bechhansen/wattzig/Software/main/kamstrup_test_data.h

#ifndef KAMSTRUP_TEST_DATA_H
#define KAMSTRUP_TEST_DATA_H

#include <stdint.h>
#include <stddef.h>

/**
 * @file kamstrup_test_data.h
 * @brief Test data for Kamstrup power meter simulation
 * 
 * This file contains example DLMS/COSEM data from a Kamstrup power meter
 * for testing and development purposes.
 */

// Test data - Kamstrup DLMS message example
static const uint8_t kamstrup_test_data[] = {
    0x7E, 0xA1, 0x2C, 0x2B, 0x21, 0x13, 0xFC, 0x04, 0xE6, 0xE7, 0x00,
    0x0F, 0x00, 0x00, 0x00, 0x00, 0x0C, 0x07, 0xE1, 0x08, 0x10, 0x03, 0x10, 0x00, 0x05, 0xFF, 0x80, 0x00, 0x00,
    0x02, 0x23,
    0x0A, 0x0E, 0x4B, 0x61, 0x6D, 0x73, 0x74, 0x72, 0x75, 0x70, 0x5F, 0x56, 0x30, 0x30, 0x30, 0x31,
    0x09, 0x06, 0x01, 0x01, 0x00, 0x00, 0x05, 0xFF, 0x0A, 0x10, 0x35, 0x37, 0x30, 0x36, 0x35, 0x36, 0x37, 0x30, 0x30, 0x30, 0x30, 0x30, 0x30, 0x30, 0x30, 0x30,
    0x09, 0x06, 0x01, 0x01, 0x60, 0x01, 0x01, 0xFF, 0x0A, 0x12, 0x30, 0x30, 0x30, 0x30, 0x30, 0x30, 0x30, 0x30, 0x30, 0x30, 0x30, 0x30, 0x30, 0x30, 0x30, 0x30, 0x30, 0x30,
    0x09, 0x06, 0x01, 0x01, 0x01, 0x07, 0x00, 0xFF, 0x06, 0x00, 0x00, 0x00, 0x00,
    0x09, 0x06, 0x01, 0x01, 0x02, 0x07, 0x00, 0xFF, 0x06, 0x00, 0x00, 0x00, 0x00,
    0x09, 0x06, 0x01, 0x01, 0x03, 0x07, 0x00, 0xFF, 0x06, 0x00, 0x00, 0x00, 0x00,
    0x09, 0x06, 0x01, 0x01, 0x04, 0x07, 0x00, 0xFF, 0x06, 0x00, 0x00, 0x00, 0x00,
    0x09, 0x06, 0x01, 0x01, 0x1F, 0x07, 0x00, 0xFF, 0x06, 0x00, 0x00, 0x00, 0x00,
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
    0x09, 0x06, 0x01, 0x01, 0x29, 0x08, 0x00, 0xFF, 0x06, 0x00, 0x0B, 0xA6, 0xE0, 0x09, 0x06, 0x01,
    0x01, 0x3D, 0x08, 0x00, 0xFF, 0x06, 0x00, 0x0F, 0x2B, 0x28, 0x23, 0x1B, 0x7E
};

// Size of the array
const int dlmsFrameSize = sizeof(dlmsFrame);

#endif /* KAMSTRUP_TEST_DATA_H */
